adjohnson00/air_quality/docs/6399-feathers3d/main_features_feathers3d.pdf

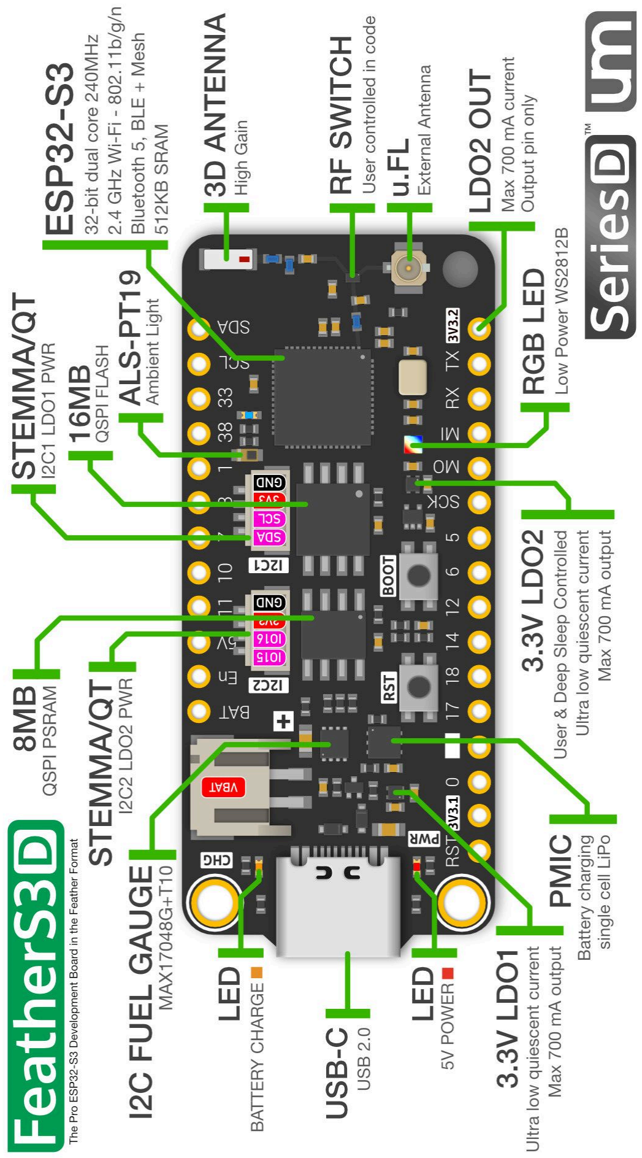
[picture p8: page 1]
